IliyanAntov/TrafficSign/Documentation/Diagrams/Code diagrams/AdminAppCodeBlockScheme.png

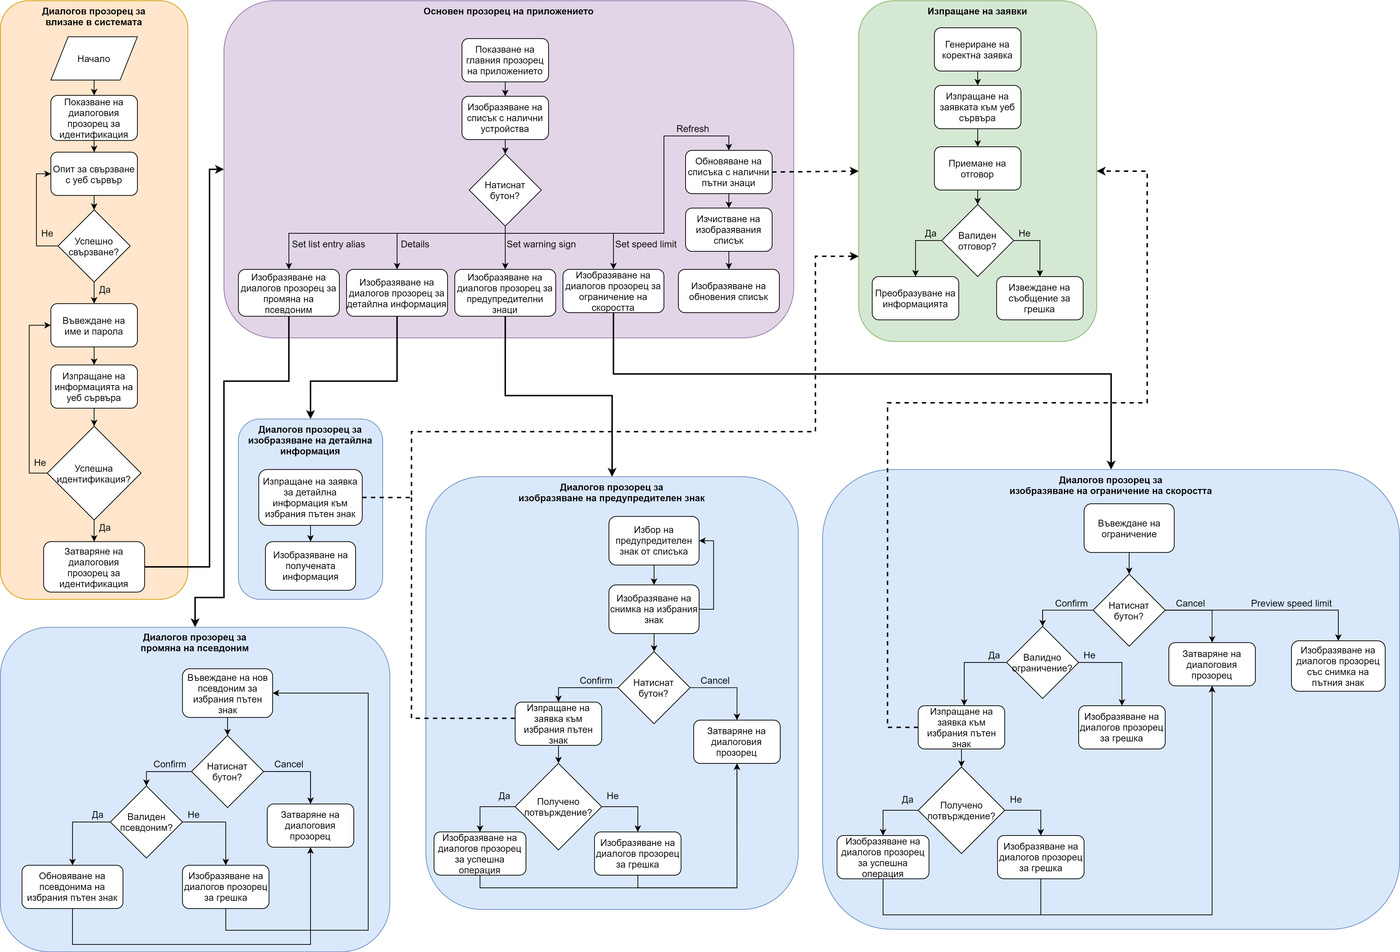
Documentation/Diagrams/Code diagrams/AdminAppCodeBlockScheme.png
