IliyanAntov/TrafficSign/Documentation/Diagrams/Code diagrams/AdminToServerBlockScheme.png

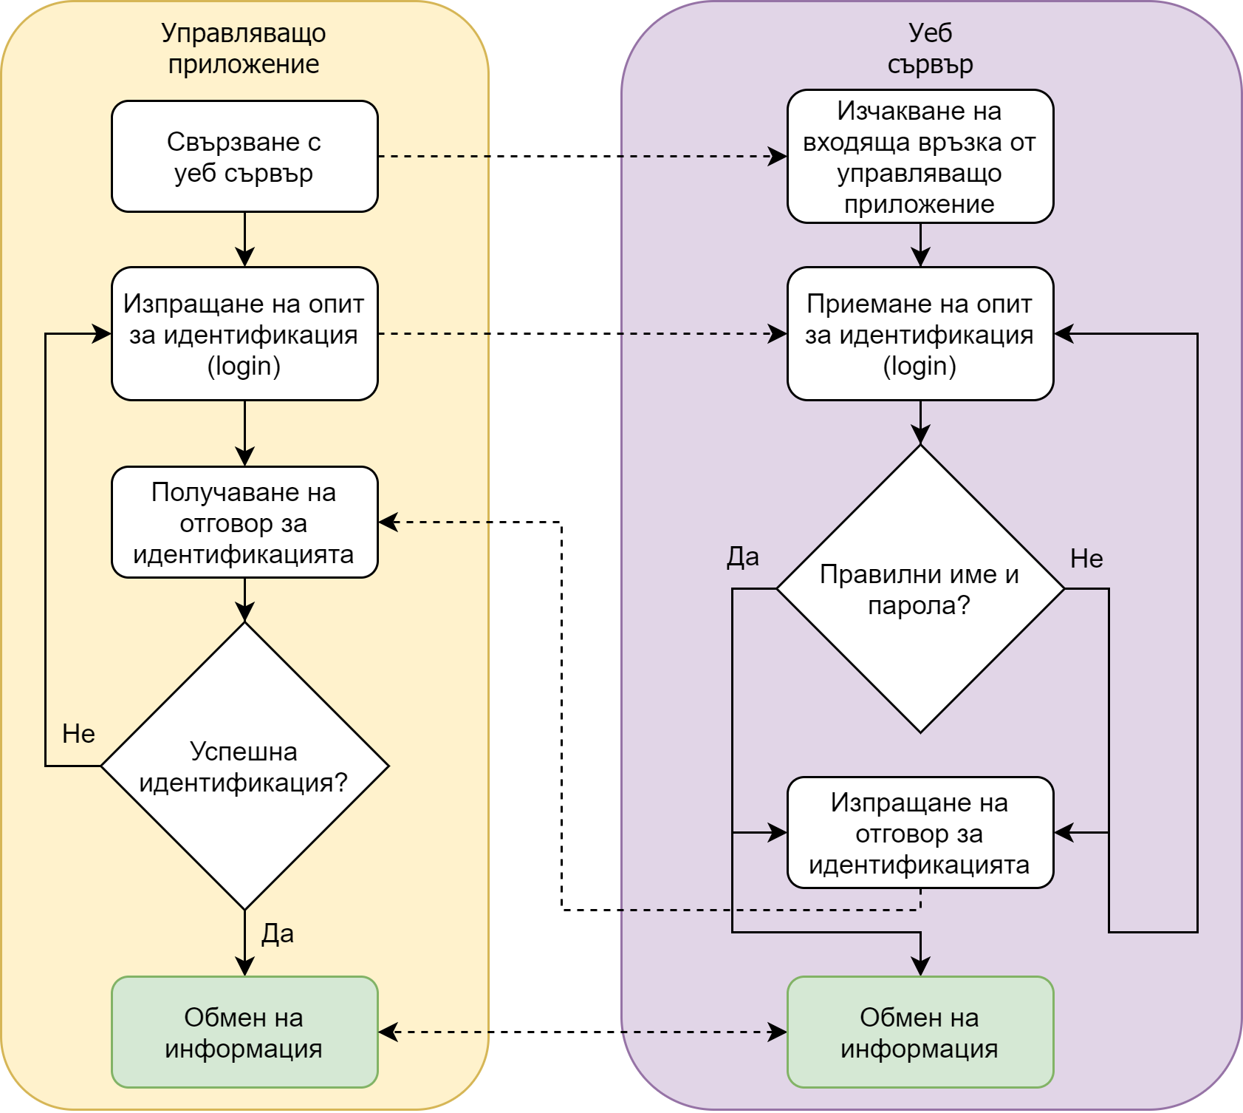
Documentation/Diagrams/Code diagrams/AdminToServerBlockScheme.png
