IliyanAntov/TrafficSign/Documentation/Diagrams/Code diagrams/MicrocontrollerCodeBlockScheme.png

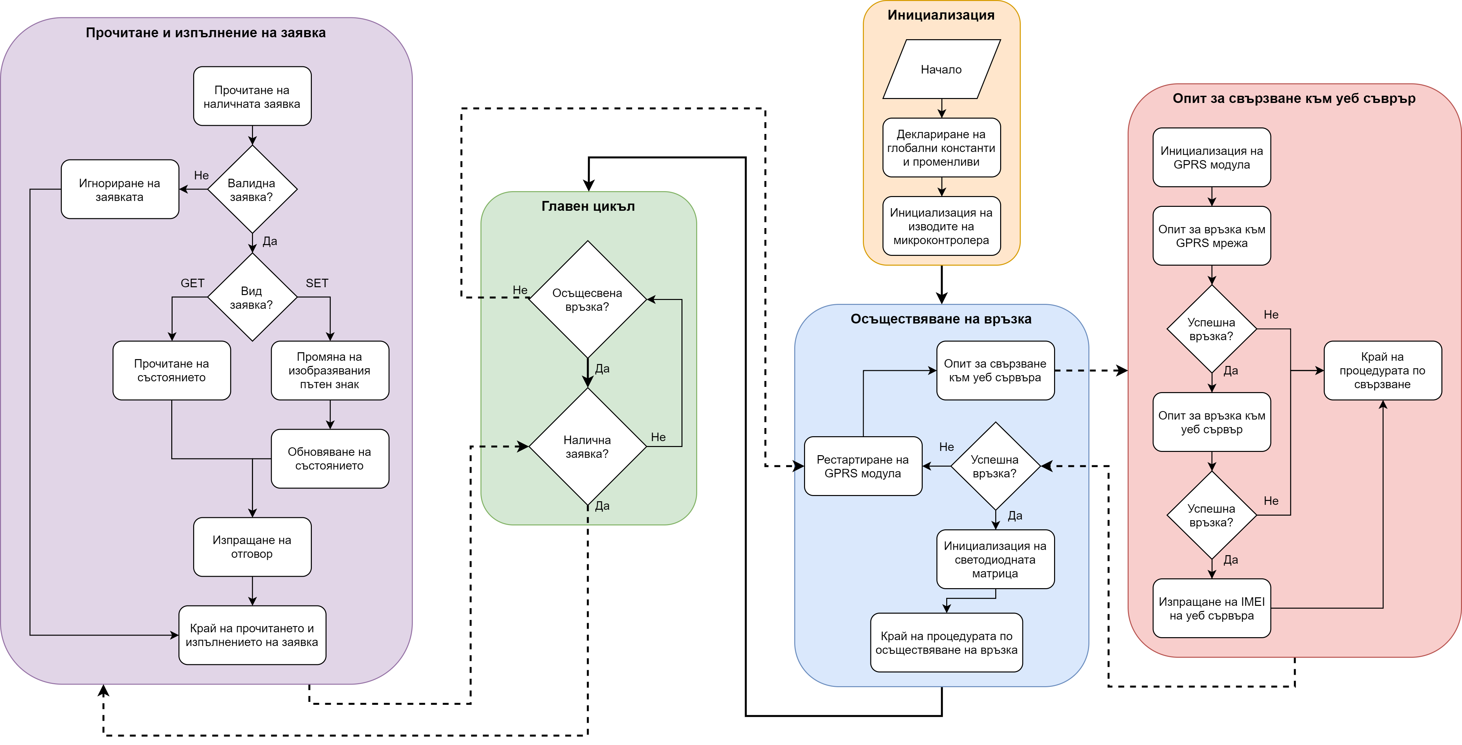
Documentation/Diagrams/Code diagrams/MicrocontrollerCodeBlockScheme.png
