IliyanAntov/TrafficSign/Documentation/Diagrams/Code diagrams/ServerCodeBlockScheme.png

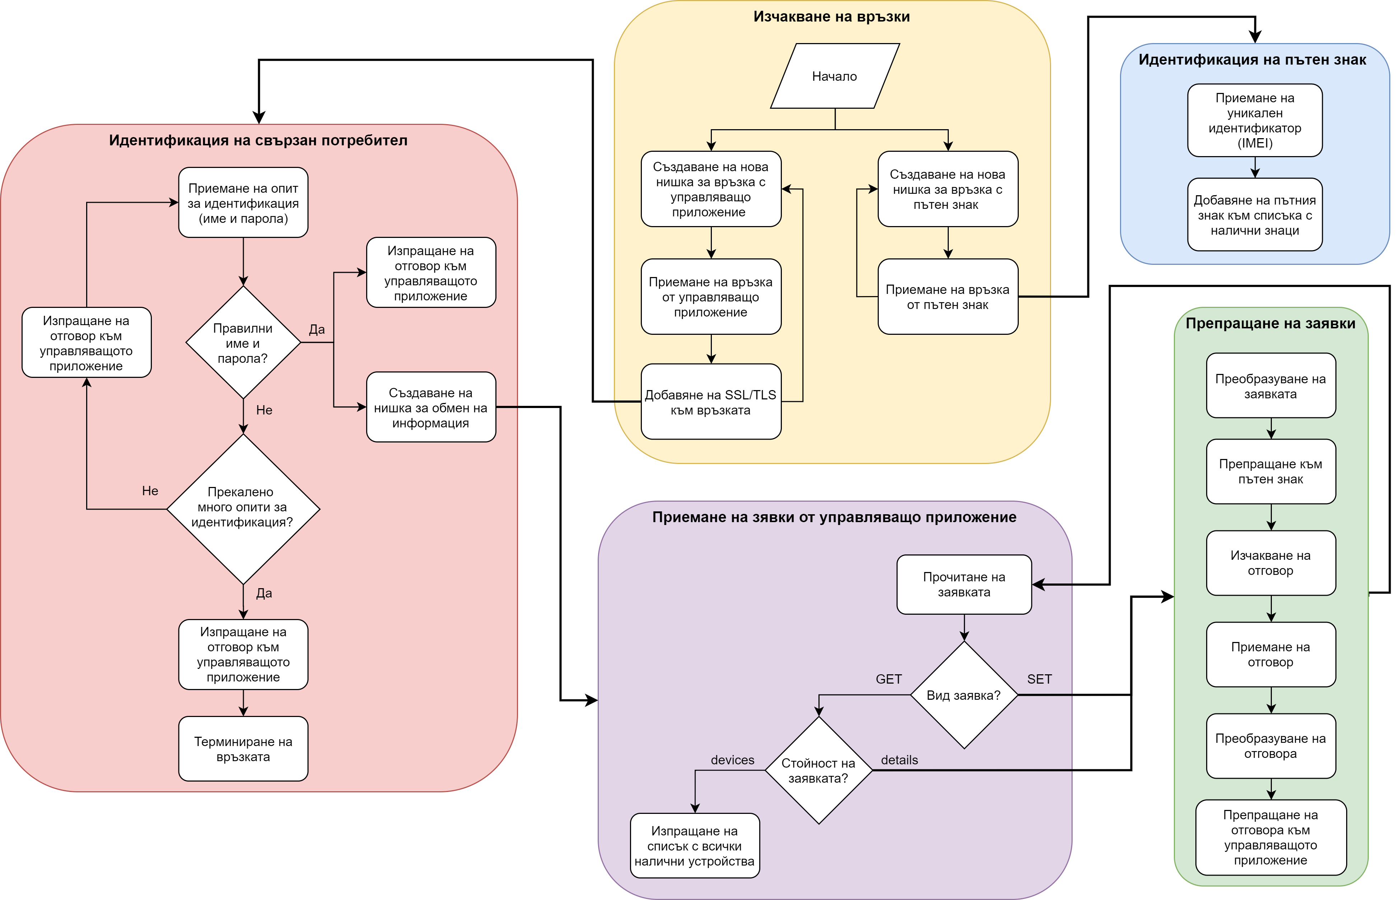
Documentation/Diagrams/Code diagrams/ServerCodeBlockScheme.png
