IliyanAntov/TrafficSign/Documentation/Diagrams/Code diagrams/ServerToDeviceBlockScheme.png

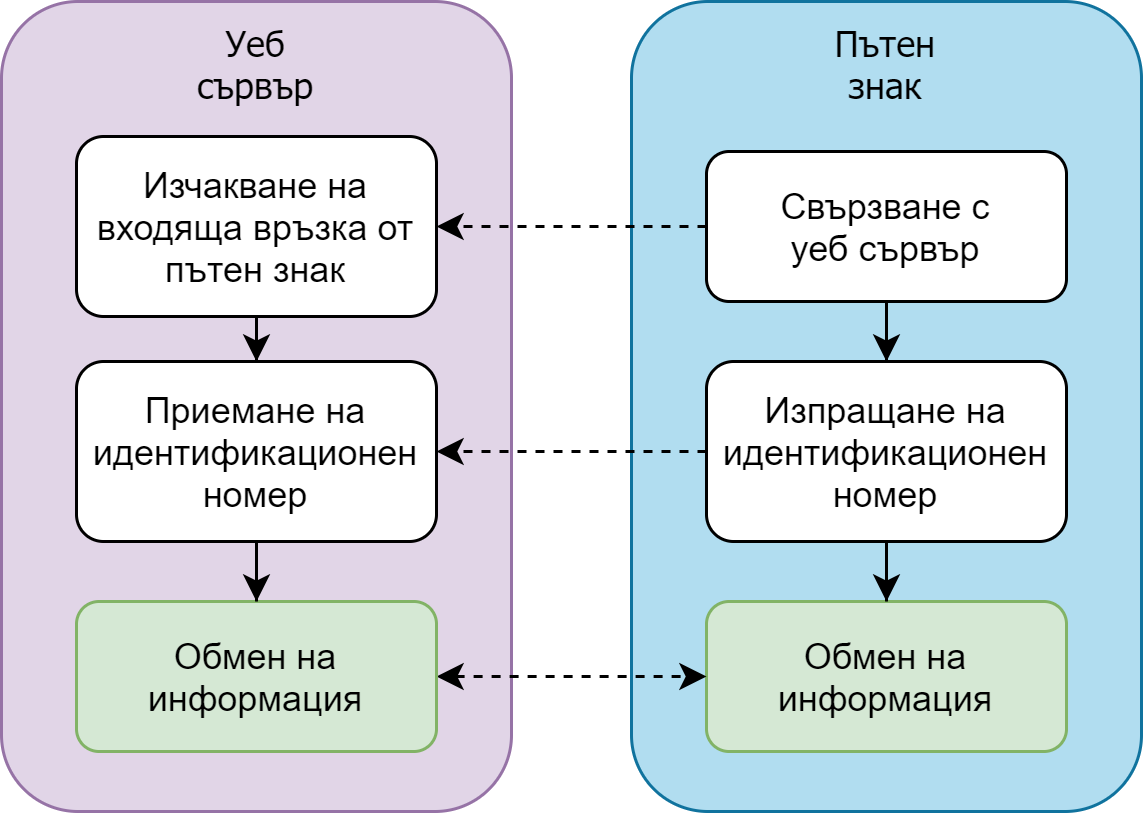
Documentation/Diagrams/Code diagrams/ServerToDeviceBlockScheme.png
