IliyanAntov/TrafficSign/Documentation/Diagrams/Functional diagrams/ChargeBlock.png

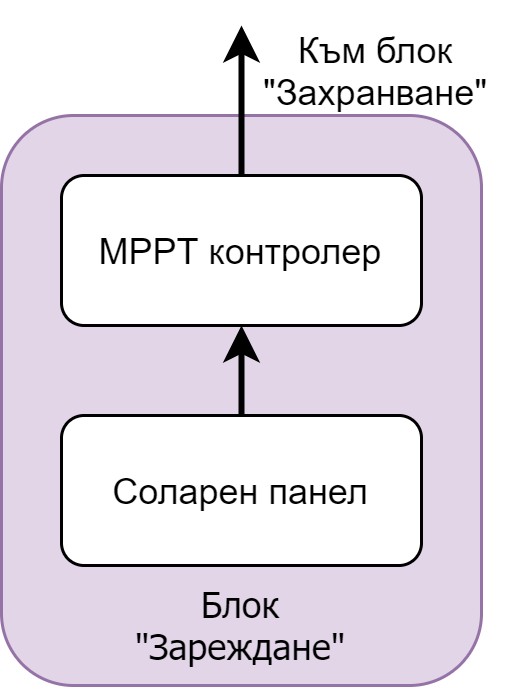
Documentation/Diagrams/Functional diagrams/ChargeBlock.png
