IliyanAntov/TrafficSign/Documentation/Diagrams/Functional diagrams/CommunicationBlock.png

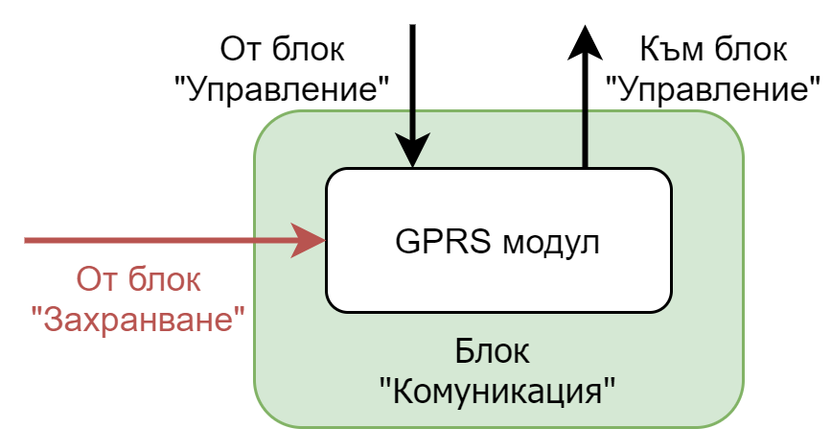
Documentation/Diagrams/Functional diagrams/CommunicationBlock.png
