IliyanAntov/TrafficSign/Documentation/Diagrams/Functional diagrams/ControlBlock.png

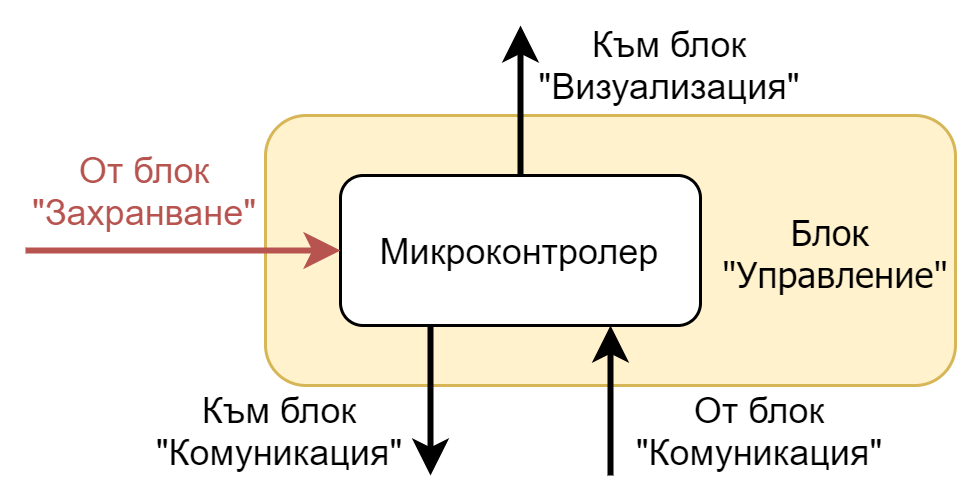
Documentation/Diagrams/Functional diagrams/ControlBlock.png
