IliyanAntov/TrafficSign/Documentation/Diagrams/Functional diagrams/FullBlockScheme.png

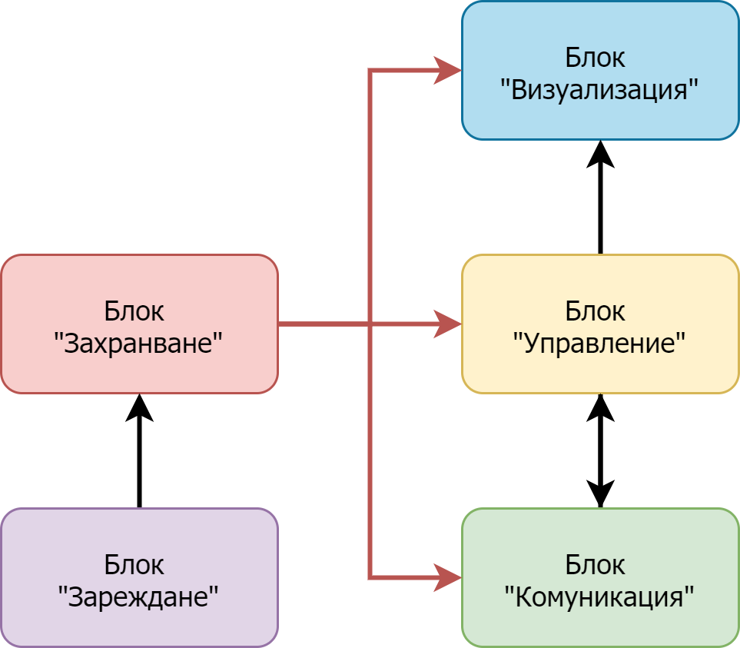
Documentation/Diagrams/Functional diagrams/FullBlockScheme.png
