IliyanAntov/TrafficSign/Documentation/Diagrams/Functional diagrams/PowerBlock.png

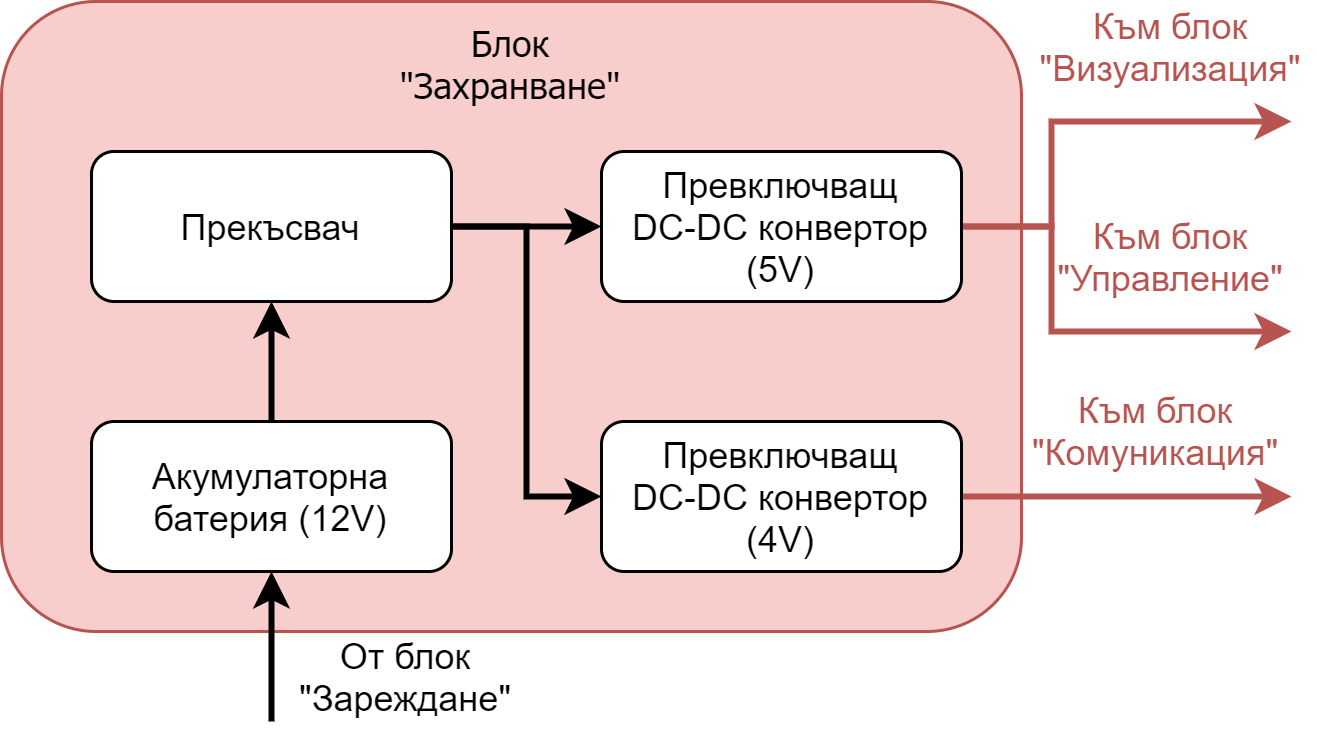
Documentation/Diagrams/Functional diagrams/PowerBlock.png
