IliyanAntov/TrafficSign/Documentation/Diagrams/Functional diagrams/VisualizationBlock.png

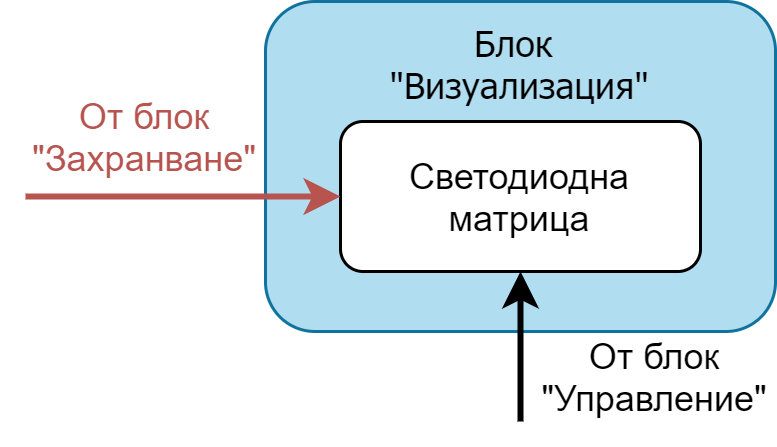
Documentation/Diagrams/Functional diagrams/VisualizationBlock.png
